jminjares4/ESP32-Sensor-Data-Logger/firmware/components/led/led.c

/**
 * @file led.c
 * @author Jesus Minjares (https://github.com/jminjares4)
 * @brief Custom LED driver source file
 * @version 0.1
 * @date 2022-07-25
 *
 * @copyright Copyright (c) 2022
 *
 */

#include "led.h"
#include "esp_idf_version.h"

#define LED_LOW 0  /*!< LED low logic */
#define LED_HIGH 1 /*!< LED high logic */

/**
 * @brief LED enable
 *
 * @param led pointer to LED object
 * @note The function assume that the user has initialize the members
 *       of the object.
 * @return None
 */
void led_enable(led_t *const led)
{
    /* Select gpio pin */
#if ESP_IDF_VERSION >= ESP_IDF_VERSION_VAL(5, 0, 0)
    esp_rom_gpio_pad_select_gpio(led->pin);
#else
    gpio_pad_select_gpio(led->pin);
#endif
    /* Set direction */
    gpio_set_direction(led->pin, GPIO_MODE_OUTPUT);
    /* Set level */
    gpio_set_level(led->pin, LED_LOW);
    /* Update state */
    led->state = (state_t)OFF;
}

/**
 * @brief Turn on LED object pin
 *
 * @param led pointer to LED object
 * @note  Function will update the state of LED
 * @return None
 */
void led_on(led_t *const led)
{
    gpio_set_level(led->pin, LED_HIGH);
    led->state = ON;
}

/**
 * @brief Turn off LED object pin
 *
 * @param led pointer to LED object
 * @note  Function will update the state of LED
 * @return None
 */
void led_off(led_t *const led)
{
    gpio_set_level(led->pin, LED_LOW);
    led->state = OFF;
}

/**
 * @brief Toggle LED object pin
 *
 * @param led pointer to LED object
 * @note  Function will update the state of LED
 * @return None
 */
void led_toggle(led_t *const led)
{
    (led->state) == ON  ? led_off(led) : led_on(led);
}
